tdouez/LoraLink/xtea.c

#include "xtea.h"

void xtea_encrypt(uint32_t* v, const uint32_t key[4]) {
    uint32_t v0 = v[0], v1 = v[1], sum = 0, delta = 0x9E3779B9;
    for (int i = 0; i < 32; i++) {
        v0 += (((v1 << 4) ^ (v1 >> 5)) + v1) ^ (sum + key[sum & 3]);
        sum += delta;
        v1 += (((v0 << 4) ^ (v0 >> 5)) + v0) ^ (sum + key[(sum>>11) & 3]);
    }
    v[0] = v0; v[1] = v1;
}

void xtea_decrypt(uint32_t* v, const uint32_t key[4]) {
    uint32_t v0 = v[0], v1 = v[1], sum = 0xC6EF3720, delta = 0x9E3779B9;
    for (int i = 0; i < 32; i++) {
        v1 -= (((v0 << 4) ^ (v0 >> 5)) + v0) ^ (sum + key[(sum>>11) & 3]);
        sum -= delta;
        v0 -= (((v1 << 4) ^ (v1 >> 5)) + v1) ^ (sum + key[sum & 3]);
    }
    v[0] = v0; v[1] = v1;
}
